techav-homebrew/MBC-1000/Mainboard/MBC-1000_Mainboard/MBC-1000_Mainboard.kicad_sch

## KiCad design Mainboard/MBC-1000_Mainboard/MBC-1000_Mainboard.kicad_sch (2025-01-16, an earlier design)

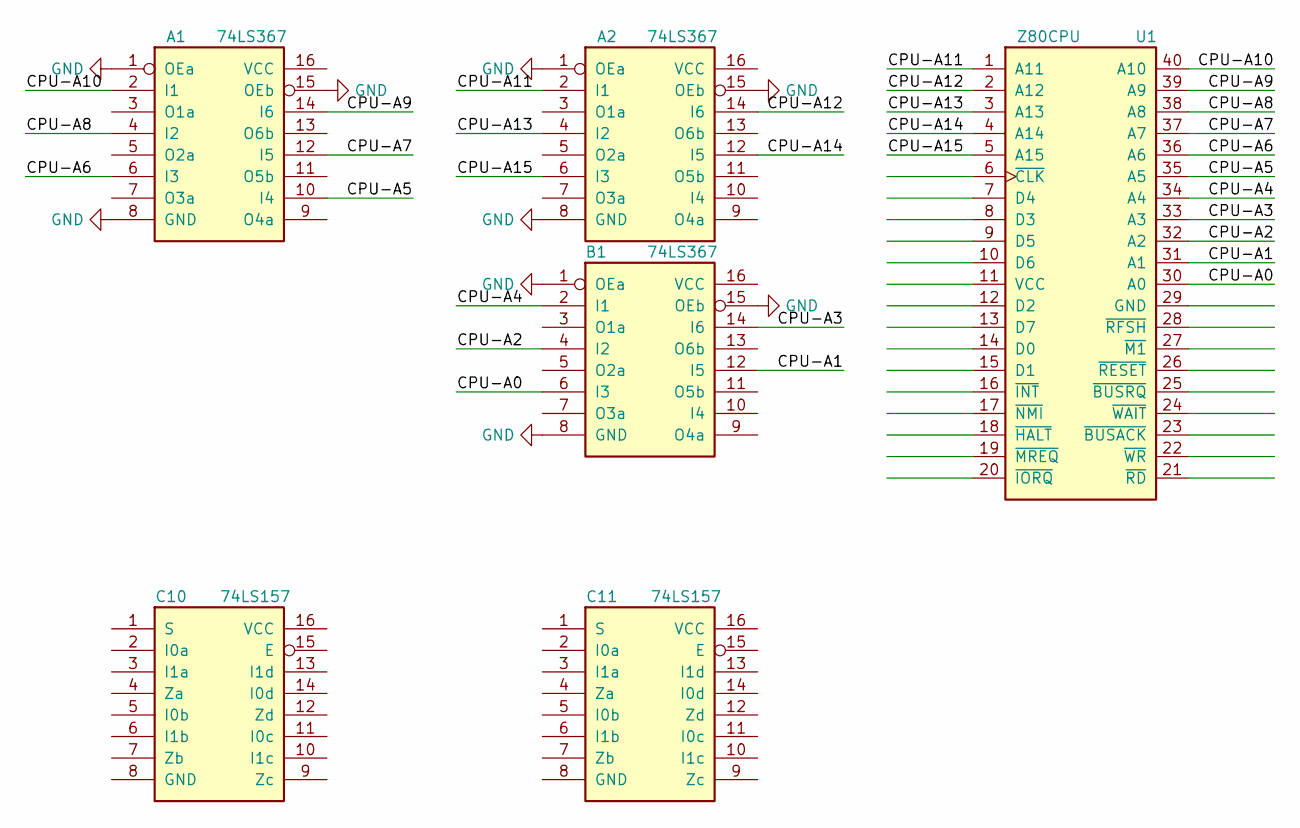
[picture p7: schematic MBC-1000_Mainboard.kicad_sch]

Parts:
A1, A2: 74LS367
B1: 74LS367
C10, C11: 74LS157
U1: Z80CPU

Connections:
CPU-A0: B1.6 (I3), U1.30 (A0)
CPU-A1: B1.12 (I5), U1.31 (A1)
CPU-A2: B1.4 (I2), U1.32 (A2)
CPU-A3: B1.14 (I6), U1.33 (A3)
CPU-A4: B1.2 (I1), U1.34 (A4)
CPU-A5: A1.10 (I4), U1.35 (A5)
CPU-A6: A1.6 (I3), U1.36 (A6)
CPU-A7: A1.12 (I5), U1.37 (A7)
CPU-A8: A1.4 (I2), U1.38 (A8)
CPU-A9: A1.14 (I6), U1.39 (A9)
CPU-A10: A1.2 (I1), U1.40 (A10)
CPU-A11: A2.2 (I1), U1.1 (A11)
CPU-A12: A2.14 (I6), U1.2 (A12)
CPU-A13: A2.4 (I2), U1.3 (A13)
CPU-A14: A2.12 (I5), U1.4 (A14)
CPU-A15: A2.6 (I3), U1.5 (A15)
GND: A1.1 (OEa), A1.8 (GND), A1.15 (OEb), A2.1 (OEa), A2.8 (GND), A2.15 (OEb), B1.1 (OEa), B1.8 (GND), B1.15 (OEb)
