techav-homebrew/MBC-1000/ExpansionCards/FS-203A/FS203A_Reverse/FS203A_Reverse.kicad_sch

## KiCad design ExpansionCards/FS-203A/FS203A_Reverse/FS203A_Reverse.kicad_sch (2023-12-20)

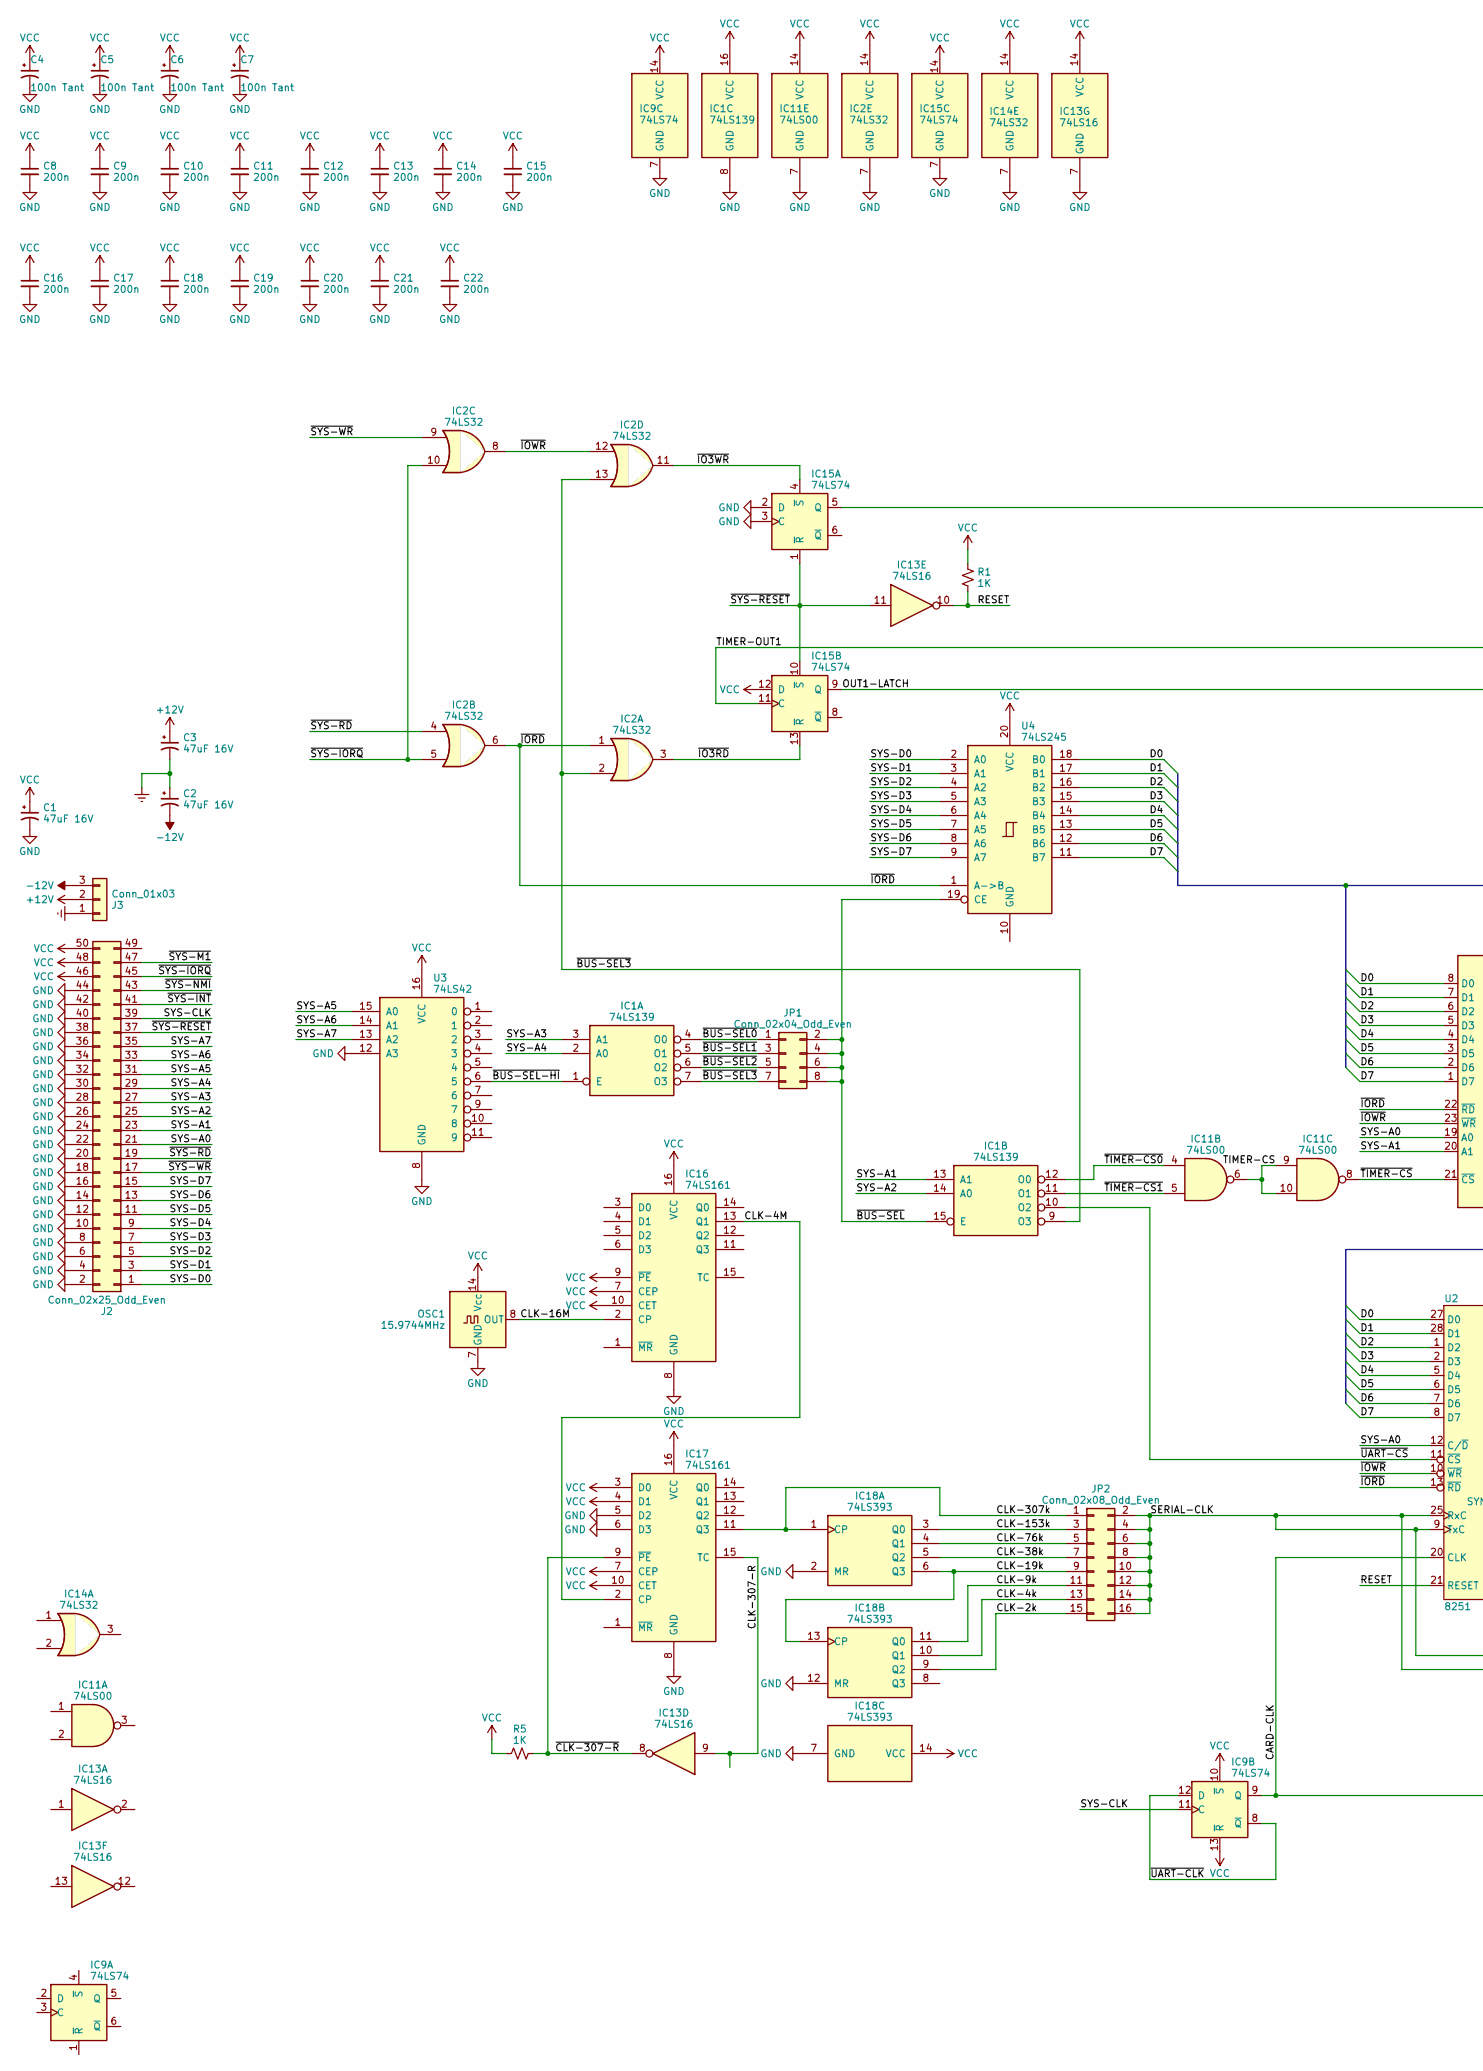
[picture p8: schematic FS203A_Reverse.kicad_sch, part in row 1, column 1]

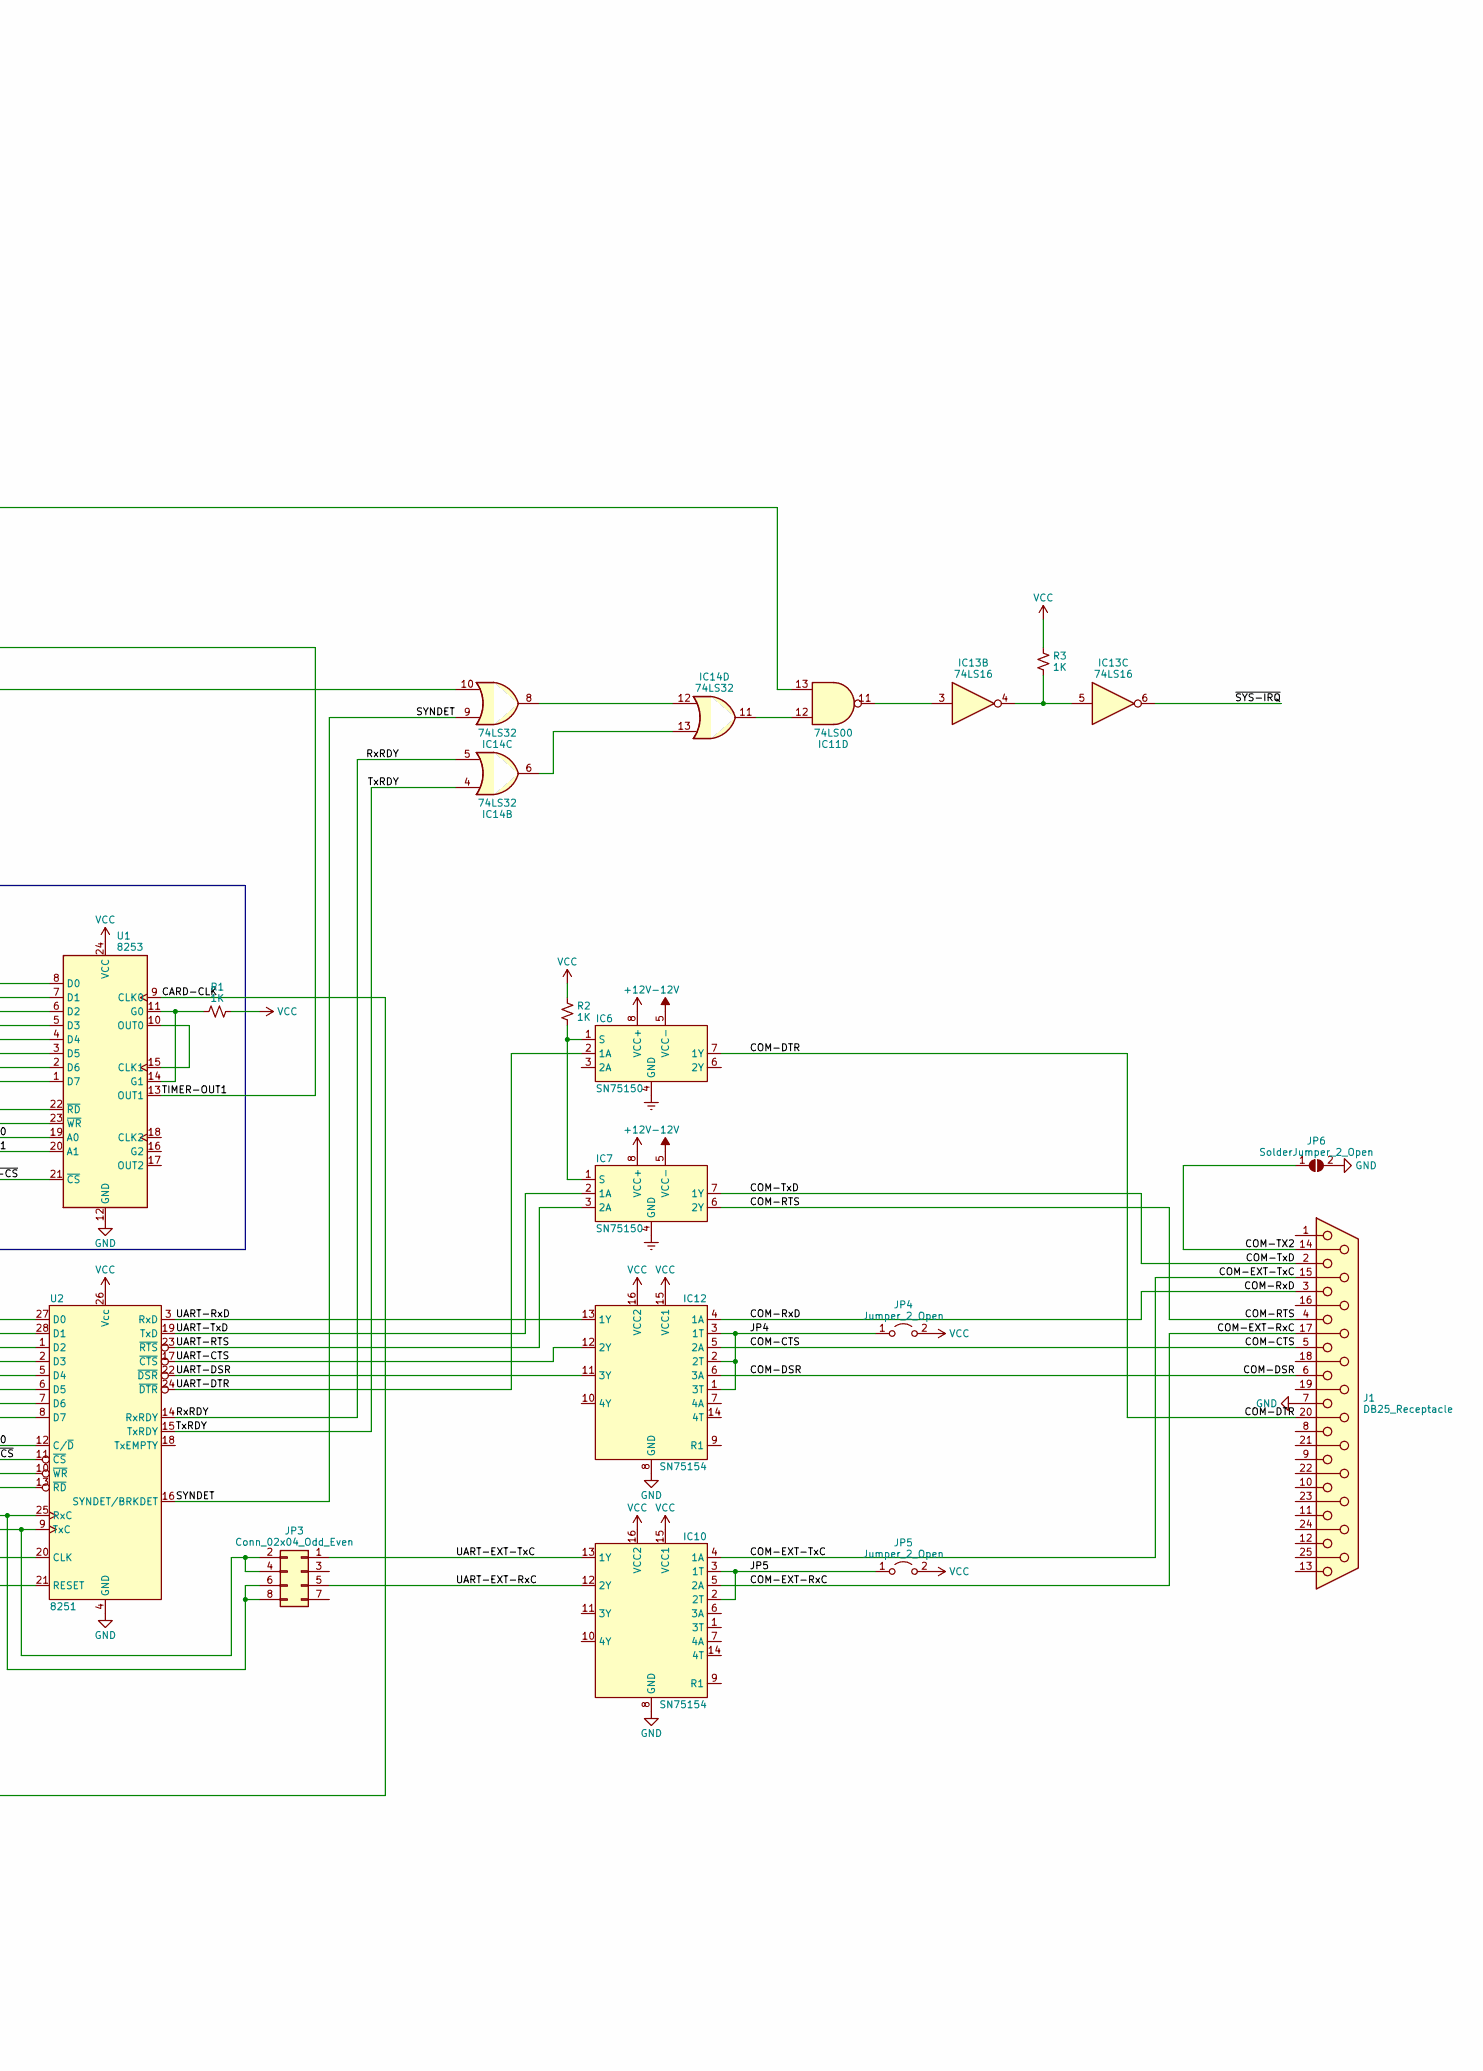
[picture p9: schematic FS203A_Reverse.kicad_sch, part in row 1, column 2]

Parts:
C1, C2, C3: 47uF 16V; CP_Radial_D6.3mm_P2.50mm
C4, C5, C6, C7: 100n Tant; C_Disc_D4.7mm_W2.5mm_P5.00mm
C8, C9, C10, C11, C12, C13, C14, C15, C16, C17, C18, C19, C20, C21, C22: 200n; C_Rect_L10.0mm_W2.5mm_P7.50mm_MKS4
IC1: 74LS139
IC2, IC14: 74LS32
IC6, IC7: SN75150
IC9, IC15: 74LS74
IC10, IC12: SN75154
IC11: 74LS00
IC13: 74LS16
IC16, IC17: 74LS161
IC18: 74LS393
J1: DB25_Receptacle
J2: Conn_02x25_Odd_Even
J3: Conn_01x03
JP1, JP3: Conn_02x04_Odd_Even
JP2: Conn_02x08_Odd_Even
JP4, JP5: Jumper_2_Open
JP6: SolderJumper_2_Open
OSC1: 15.9744MHz; Oscillator_DIP-14
R1, R2, R3, R5: 1K
U1: 8253; DIP-24_W15.24mm
U2: 8251
U3: 74LS42
U4: 74LS245

Connections:
+12V: C3.1, IC6.8 (VCC+), IC7.8 (VCC+), J3.2
-12V: C2.2, IC6.5 (VCC-), IC7.5 (VCC-), J3.3
CARD-CLK: IC9.9 (Q), U1.9 (CLK0), U2.20 (CLK)
CLK-2k: IC18.9 (Q2), JP2.15
CLK-4M: IC16.13 (Q1), IC17.2 (CP)
CLK-4k: IC18.10 (Q1), JP2.13
CLK-9k: IC18.11 (Q0), JP2.11
CLK-16M: IC16.2 (CP), OSC1.8 (OUT)
CLK-19k: IC18.6 (Q3), IC18.13 (CP), JP2.9
CLK-38k: IC18.5 (Q2), JP2.7
CLK-76k: IC18.4 (Q1), JP2.5
CLK-153k: IC18.3 (Q0), JP2.3
CLK-307-R: IC13.9, IC17.15 (TC)
CLK-307k: IC17.11 (Q3), IC18.1 (CP), JP2.1
COM-CTS: IC12.5 (2A), J1.5
COM-DSR: IC12.6 (3A), J1.6
COM-DTR: IC6.7 (1Y), J1.20
COM-EXT-RxC: IC10.5 (2A), J1.17
COM-EXT-TxC: IC10.4 (1A), J1.15
COM-RTS: IC7.6 (2Y), J1.4
COM-RxD: IC12.4 (1A), J1.3
COM-TX2: J1.14, JP6.1 (A)
COM-TxD: IC7.7 (1Y), J1.2
D0: U1.8 (D0), U2.27 (D0), U4.18 (B0)
D1: U1.7 (D1), U2.28 (D1), U4.17 (B1)
D2: U1.6 (D2), U2.1 (D2), U4.16 (B2)
D3: U1.5 (D3), U2.2 (D3), U4.15 (B3)
D4: U1.4 (D4), U2.5 (D4), U4.14 (B4)
D5: U1.3 (D5), U2.6 (D5), U4.13 (B5)
D6: U1.2 (D6), U2.7 (D6), U4.12 (B6)
D7: U1.1 (D7), U2.8 (D7), U4.11 (B7)
Earth: C2.1, C3.2, IC6.4 (GND), IC7.4 (GND), J3.1
GND: C1.2, C4.2, C5.2, C6.2, C7.2, C8.2, C9.2, C10.2, C11.2, C12.2, C13.2, C14.2, C15.2, C16.2, C17.2, C18.2, C19.2, C20.2, C21.2, C22.2, IC1.8 (GND), IC2.7 (GND), IC9.7 (GND), IC10.8 (GND), IC11.7 (GND), IC12.8 (GND), IC13.7 (GND), IC14.7 (GND), IC15.2 (D), IC15.3 (C), IC15.7 (GND), IC16.8 (GND), IC17.5 (D2), IC17.6 (D3), IC17.8 (GND), IC18.2 (MR), IC18.7 (GND), IC18.12 (MR), J1.7, J2.2, J2.4, J2.10, J2.12, J2.14, J2.16, J2.18, J2.20, J2.22, J2.24, J2.26, J2.28, J2.30, J2.32, J2.34, J2.36, J2.38, J2.40, J2.42, J2.44, JP6.2 (B), OSC1.7 (GND), U1.12 (GND), U2.4 (GND), U3.8 (GND), U3.12 (A3)
JP4: IC12.1 (3T), IC12.2 (2T), IC12.3 (1T), JP4.1 (A)
JP5: IC10.2 (2T), IC10.3 (1T), JP5.1 (A)
unnamed: IC6.1 (S), IC7.1 (S), R2.1
unnamed: IC11.11, IC13.3
unnamed: IC11.12, IC14.11
unnamed: IC11.13, IC15.5 (Q)
unnamed: IC13.4, IC13.5, R3.2
unnamed: IC14.8, IC14.12
unnamed: IC14.6, IC14.13
unnamed: R1.1, U1.11 (G0), U1.14 (G1)
unnamed: U1.10 (OUT0), U1.15 (CLK1)
OUT1-LATCH: IC14.10, IC15.9 (Q)
RESET: IC13.10, R1.2, U2.21 (RESET)
RxRDY: IC14.5, U2.14 (RxRDY)
SERIAL-CLK: JP2.2, JP2.4, JP2.6, JP2.8, JP2.10, JP2.12, JP2.14, JP2.16, JP3.2, JP3.4, JP3.6, JP3.8, U2.9 (TxC), U2.25 (RxC)
SYNDET: IC14.9, U2.16 (SYNDET/BRKDET)
SYS-A0: J2.21, U1.19 (A0), U2.12 (C/~D)
SYS-A1: IC1.13 (A1), J2.23, U1.20 (A1)
SYS-A2: IC1.14 (A0), J2.25
SYS-A3: IC1.3 (A1), J2.27
SYS-A4: IC1.2 (A0), J2.29
SYS-A5: J2.31, U3.15 (A0)
SYS-A6: J2.33, U3.14 (A1)
SYS-A7: J2.35, U3.13 (A2)
SYS-CLK: IC9.11 (C), J2.39
SYS-D0: J2.1, U4.2 (A0)
SYS-D1: J2.3, U4.3 (A1)
SYS-D2: J2.5, U4.4 (A2)
SYS-D3: J2.7, U4.5 (A3)
SYS-D4: J2.9, U4.6 (A4)
SYS-D5: J2.11, U4.7 (A5)
SYS-D6: J2.13, U4.8 (A6)
SYS-D7: J2.15, U4.9 (A7)
TIMER-CS: IC11.6, IC11.9, IC11.10
TIMER-OUT1: IC15.11 (C), U1.13 (OUT1)
TxRDY: IC14.4, U2.15 (TxRDY)
UART-CTS: IC12.12 (2Y), U2.17 (~CTS)
UART-DSR: IC12.11 (3Y), U2.22 (~DSR)
UART-DTR: IC6.2 (1A), U2.24 (~DTR)
UART-EXT-RxC: IC10.12 (2Y), JP3.5
UART-EXT-TxC: IC10.13 (1Y), JP3.1
UART-RTS: IC7.3 (2A), U2.23 (~RTS)
UART-RxD: IC12.13 (1Y), U2.3 (RxD)
UART-TxD: IC7.2 (1A), U2.19 (TxD)
VCC: C1.1, C4.1, C5.1, C6.1, C7.1, C8.1, C9.1, C10.1, C11.1, C12.1, C13.1, C14.1, C15.1, C16.1, C17.1, C18.1, C19.1, C20.1, C21.1, C22.1, IC1.16 (VCC), IC2.14 (VCC), IC9.10 (~S), IC9.13 (~R), IC9.14 (VCC), IC10.15 (VCC1), IC10.16 (VCC2), IC11.14 (VCC), IC12.15 (VCC1), IC12.16 (VCC2), IC13.14 (VCC), IC14.14 (VCC), IC15.12 (D), IC15.14 (VCC), IC16.7 (CEP), IC16.9 (~PE), IC16.10 (CET), IC16.16 (VCC), IC17.3 (D0), IC17.4 (D1), IC17.7 (CEP), IC17.10 (CET), IC17.16 (VCC), IC18.14 (VCC), J2.46, J2.48, J2.50, JP4.2 (B), JP5.2 (B), OSC1.14 (Vcc), R1.1, R1.2, R2.2, R3.1, R5.1, U1.24 (VCC), U2.26 (Vcc), U3.16 (VCC), U4.20 (VCC)
~BUS-SEL0: IC1.4 (O0), JP1.1
~BUS-SEL1: IC1.5 (O1), JP1.3
~BUS-SEL2: IC1.6 (O2), JP1.5
~BUS-SEL3: IC1.7 (O3), IC1.9 (O3), IC2.2, IC2.13, JP1.7
~BUS-SEL-HI: IC1.1 (E), U3.6 (5)
~BUS-SEL: IC1.15 (E), JP1.2, JP1.4, JP1.6, JP1.8, U4.19 (CE)
~CLK-307-R: IC13.8, IC17.9 (~PE), R5.2
~IO3RD: IC2.3, IC15.13 (~R)
~IO3WR: IC2.11, IC15.4 (~S)
~IORD: IC2.1, IC2.6, U1.22 (~RD), U2.13 (~RD), U4.1 (A->B)
~IOWR: IC2.8, IC2.12, U1.23 (~WR), U2.10 (~WR)
~SYS-INT: J2.41
~SYS-IORQ: IC2.5, IC2.10, J2.45
~SYS-IRQ: IC13.6
~SYS-M1: J2.47
~SYS-NMI: J2.43
~SYS-RD: IC2.4, J2.19
~SYS-RESET: IC13.11, IC15.1 (~R), IC15.10 (~S), J2.37
~SYS-WR: IC2.9, J2.17
~TIMER-CS0: IC1.12 (O0), IC11.4
~TIMER-CS1: IC1.11 (O1), IC11.5
~TIMER-CS: IC11.8, U1.21 (~CS)
~UART-CLK: IC9.8 (~Q), IC9.12 (D)
~UART-CS: IC1.10 (O2), U2.11 (~CS)
